plane-watch/hardware/planewatcher/analysis/frontend-sensitivity-2026-09/plots/adc-window-61.png

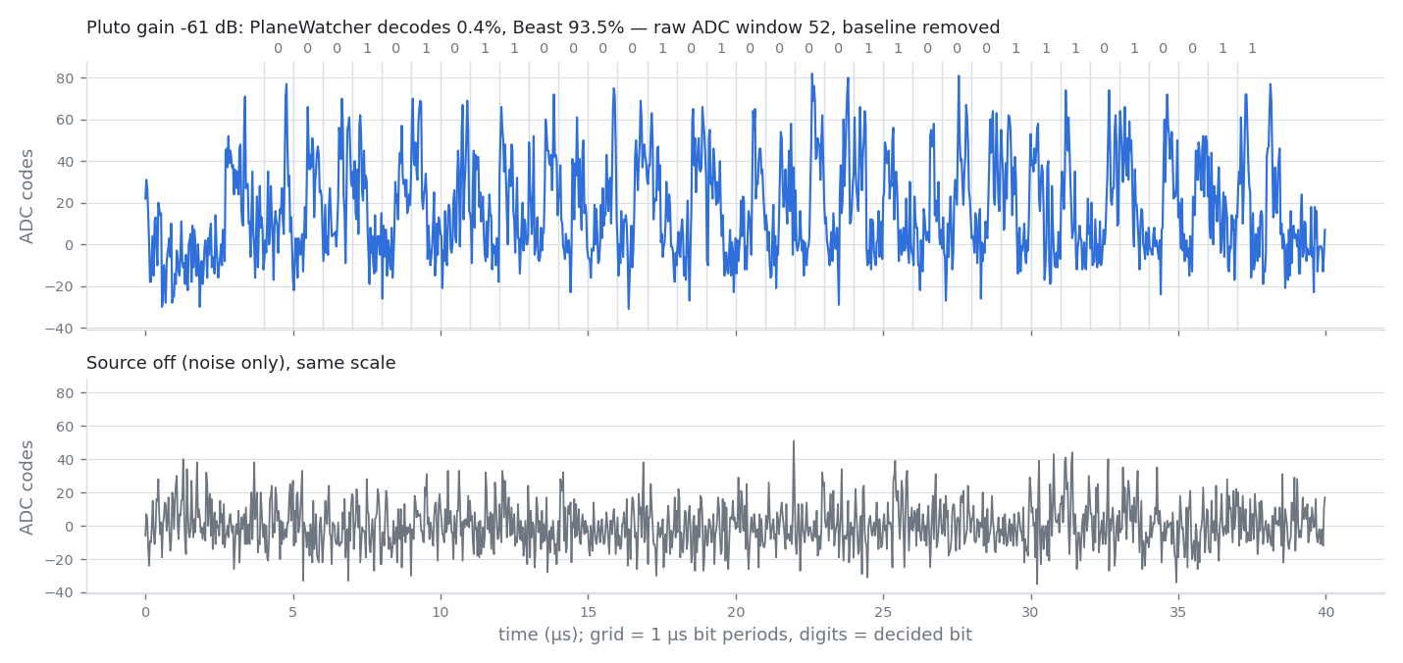
planewatcher/analysis/frontend-sensitivity-2026-09/plots/adc-window-61.png
